wdq/SensorSeed/SensorSeed/Arduino/ArduinoFeather/sketch_jul08b/sketch_jul08b.ino

/*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
// Licence can be viewed at                               
// http://www.gnu.org/licenses/gpl-3.0.txt
//
// Please maintain this license information along with authorship
// and copyright notices in any redistribution of this code
// **********************************************************************************/

#include <RFM69.h>    //get it here: https://www.github.com/lowpowerlab/rfm69
#include <SPI.h>

//*********************************************************************************************
// *********** IMPORTANT SETTINGS - YOU MUST CHANGE/ONFIGURE TO FIT YOUR HARDWARE *************
//*********************************************************************************************
#define NETWORKID     100  //the same on all nodes that talk to each other
#define NODEID        1  

//Match frequency to the hardware version of the radio on your Feather
//#define FREQUENCY     RF69_433MHZ
//#define FREQUENCY     RF69_868MHZ
#define FREQUENCY      RF69_915MHZ
#define ENCRYPTKEY     "sampleEncryptKey" //exactly the same 16 characters/bytes on all nodes!
#define IS_RFM69HCW    true // set to 'true' if you are using an RFM69HCW module

//*********************************************************************************************
#define SERIAL_BAUD   115200

#define RFM95_CS 8
#define RFM95_RST 4
#define RFM95_INT 3

#define LED           13  // onboard blinky

int16_t packetnum = 0;  // packet counter, we increment per xmission

RFM69 radio = RFM69(RFM95_CS, RFM95_INT);

void setup() {
  while (!Serial); // wait until serial console is open, remove if not tethered to computer
  Serial.begin(SERIAL_BAUD);

  Serial.println("Feather RFM69HCW Receiver");
  
  // Hard Reset the RFM module
  pinMode(RFM95_RST, OUTPUT);
  digitalWrite(RFM95_RST, HIGH);
  delay(100);
  digitalWrite(RFM95_RST, LOW);
  delay(100);
  
  // Initialize radio
  radio.initialize(FREQUENCY,NODEID,NETWORKID);
  if (IS_RFM69HCW) {
    radio.setHighPower();    // Only for RFM69HCW & HW!
  }
  radio.setPowerLevel(31); // power output ranges from 0 (5dBm) to 31 (20dBm)
  
  radio.encrypt(ENCRYPTKEY);
  
  pinMode(LED, OUTPUT);

  Serial.print("\nListening at ");
  Serial.print(FREQUENCY==RF69_433MHZ ? 433 : FREQUENCY==RF69_868MHZ ? 868 : 915);
  Serial.println(" MHz");
}

void loop() {
  //check if something was received (could be an interrupt from the radio)
  if (radio.receiveDone())
  {
    //print message received to serial
    Serial.print('[');Serial.print(radio.SENDERID);Serial.print("] ");
    Serial.print((char*)radio.DATA);
    Serial.print("   [RX_RSSI:");Serial.print(radio.RSSI);Serial.print("]");

    //check if received message contains Hello World
    if (strstr((char *)radio.DATA, "Hello World"))
    {
      //check if sender wanted an ACK
      if (radio.ACKRequested())
      {
        radio.sendACK();
        Serial.println(" - ACK sent");
      }
      Blink(LED, 40, 3); //blink LED 3 times, 40ms between blinks
    }  
  }

  radio.receiveDone(); //put radio in RX mode
  Serial.flush(); //make sure all serial data is clocked out before sleeping the MCU
}

void Blink(byte PIN, byte DELAY_MS, byte loops)
{
  for (byte i=0; i<loops; i++)
  {
    digitalWrite(PIN,HIGH);
    delay(DELAY_MS);
    digitalWrite(PIN,LOW);
    delay(DELAY_MS);
  }
}
